jerry20091103/Teensy_Grovebox/Teensy_Grovebox_CODE/src/Audio/AudioSynth.cpp

#include "AudioSynth.h"
#include "AudioIO.h"
#include "SF2_Samples/SF2_Samples.h"
#include "AudioUtility.h"

AudioSynth_ AudioSynth;

AudioSynth_::ModParamList::ModParamList(AudioVoice *voiceArr) : oscPitchOffset{OscPitchOffset(voiceArr, 0), OscPitchOffset(voiceArr, 1)},
                                                                oscLevel{OscLevel(voiceArr, 0), OscLevel(voiceArr, 1)},
                                                                oscPwm{OscPwm(voiceArr, 0), OscPwm(voiceArr, 1)},
                                                                noiseLevel(voiceArr),
                                                                filterCutoff(voiceArr),
                                                                filterResonance(voiceArr),
                                                                lfoFreq{LfoFreq(voiceArr, 0), LfoFreq(voiceArr, 1)},
                                                                lfoLevel{LfoLevel(voiceArr, 0), LfoLevel(voiceArr, 1)},
                                                                envDelay{EnvDelay(voiceArr, 0), EnvDelay(voiceArr, 1), EnvDelay(voiceArr, 2)},
                                                                envAttack{EnvAttack(voiceArr, 0), EnvAttack(voiceArr, 1), EnvAttack(voiceArr, 2)},
                                                                envDecay{EnvDecay(voiceArr, 0), EnvDecay(voiceArr, 1), EnvDecay(voiceArr, 2)},
                                                                envSustain{EnvSustain(voiceArr, 0), EnvSustain(voiceArr, 1), EnvSustain(voiceArr, 2)},
                                                                envRelease{EnvRelease(voiceArr, 0), EnvRelease(voiceArr, 1), EnvRelease(voiceArr, 2)},
                                                                clipLevel(voiceArr)
{
}

AudioSynth_::AudioSynth_()
    : modParamList(voiceArr)
{
    // set up voice mixers
    voiceMixer[0] = &voiceMixer0_0;
    voiceMixer[1] = &voiceMixer0_1;

    for (auto i : voiceMixer)
    {
        i->gain(0, 0.25);
        i->gain(1, 0.25);
        i->gain(2, 0.25);
        i->gain(3, 0.25);
    }

    voiceFinalMixer = &voiceMixer1_0;

    voiceFinalMixer->gain(0, 0.5);
    voiceFinalMixer->gain(1, 0.5);

    // setup master volume
    mainVolume[0] = &ampInsOutL;
    mainVolume[1] = &ampInsOutR;

    // *initiailze all voices
    // wavetable synth
    voiceArr[0].waveTable = &wavetable0;
    voiceArr[1].waveTable = &wavetable1;
    voiceArr[2].waveTable = &wavetable2;
    voiceArr[3].waveTable = &wavetable3;
    voiceArr[4].waveTable = &wavetable4;
    voiceArr[5].waveTable = &wavetable5;
    voiceArr[6].waveTable = &wavetable6;
    voiceArr[7].waveTable = &wavetable7;
    // 2 waveforms
    voiceArr[0].waveform[0] = &waveform0_0;
    voiceArr[0].waveform[1] = &waveform0_1;
    voiceArr[1].waveform[0] = &waveform1_0;
    voiceArr[1].waveform[1] = &waveform1_1;
    voiceArr[2].waveform[0] = &waveform2_0;
    voiceArr[2].waveform[1] = &waveform2_1;
    voiceArr[3].waveform[0] = &waveform3_0;
    voiceArr[3].waveform[1] = &waveform3_1;
    voiceArr[4].waveform[0] = &waveform4_0;
    voiceArr[4].waveform[1] = &waveform4_1;
    voiceArr[5].waveform[0] = &waveform5_0;
    voiceArr[5].waveform[1] = &waveform5_1;
    voiceArr[6].waveform[0] = &waveform6_0;
    voiceArr[6].waveform[1] = &waveform6_1;
    voiceArr[7].waveform[0] = &waveform7_0;
    voiceArr[7].waveform[1] = &waveform7_1;
    // noise generator
    voiceArr[0].noise = &noise0;
    voiceArr[1].noise = &noise1;
    voiceArr[2].noise = &noise2;
    voiceArr[3].noise = &noise3;
    voiceArr[4].noise = &noise4;
    voiceArr[5].noise = &noise5;
    voiceArr[6].noise = &noise6;
    voiceArr[7].noise = &noise7;
    // playClip (sample player)
    voiceArr[0].playClip = &playClip0;
    voiceArr[1].playClip = &playClip1;
    voiceArr[2].playClip = &playClip2;
    voiceArr[3].playClip = &playClip3;
    voiceArr[4].playClip = &playClip4;
    voiceArr[5].playClip = &playClip5;
    voiceArr[6].playClip = &playClip6;
    voiceArr[7].playClip = &playClip7;
    // clip amp (sampler volume)
    voiceArr[0].clipAmp = &clipAmp0;
    voiceArr[1].clipAmp = &clipAmp1;
    voiceArr[2].clipAmp = &clipAmp2;
    voiceArr[3].clipAmp = &clipAmp3;
    voiceArr[4].clipAmp = &clipAmp4;
    voiceArr[5].clipAmp = &clipAmp5;
    voiceArr[6].clipAmp = &clipAmp6;
    voiceArr[7].clipAmp = &clipAmp7;
    // voice mode switch
    voiceArr[0].voiceSwitch = &voiceSwitch0;
    voiceArr[1].voiceSwitch = &voiceSwitch1;
    voiceArr[2].voiceSwitch = &voiceSwitch2;
    voiceArr[3].voiceSwitch = &voiceSwitch3;
    voiceArr[4].voiceSwitch = &voiceSwitch4;
    voiceArr[5].voiceSwitch = &voiceSwitch5;
    voiceArr[6].voiceSwitch = &voiceSwitch6;
    voiceArr[7].voiceSwitch = &voiceSwitch7;
    // ladder filter
    voiceArr[0].ladderFilter = &ladder0;
    voiceArr[1].ladderFilter = &ladder1;
    voiceArr[2].ladderFilter = &ladder2;
    voiceArr[3].ladderFilter = &ladder3;
    voiceArr[4].ladderFilter = &ladder4;
    voiceArr[5].ladderFilter = &ladder5;
    voiceArr[6].ladderFilter = &ladder6;
    voiceArr[7].ladderFilter = &ladder7;
    // lfo1
    voiceArr[0].lfo[0] = &lfo0_0;
    voiceArr[1].lfo[0] = &lfo1_0;
    voiceArr[2].lfo[0] = &lfo2_0;
    voiceArr[3].lfo[0] = &lfo3_0;
    voiceArr[4].lfo[0] = &lfo4_0;
    voiceArr[5].lfo[0] = &lfo5_0;
    voiceArr[6].lfo[0] = &lfo6_0;
    voiceArr[7].lfo[0] = &lfo7_0;
    // lfo2
    voiceArr[0].lfo[1] = &lfo0_1;
    voiceArr[1].lfo[1] = &lfo1_1;
    voiceArr[2].lfo[1] = &lfo2_1;
    voiceArr[3].lfo[1] = &lfo3_1;
    voiceArr[4].lfo[1] = &lfo4_1;
    voiceArr[5].lfo[1] = &lfo5_1;
    voiceArr[6].lfo[1] = &lfo6_1;
    voiceArr[7].lfo[1] = &lfo7_1;
    // amp envelope
    voiceArr[0].env[0] = &ampEnvelope0;
    voiceArr[1].env[0] = &ampEnvelope1;
    voiceArr[2].env[0] = &ampEnvelope2;
    voiceArr[3].env[0] = &ampEnvelope3;
    voiceArr[4].env[0] = &ampEnvelope4;
    voiceArr[5].env[0] = &ampEnvelope5;
    voiceArr[6].env[0] = &ampEnvelope6;
    voiceArr[7].env[0] = &ampEnvelope7;
    // env1
    voiceArr[0].env[1] = &envelope0_0;
    voiceArr[1].env[1] = &envelope1_0;
    voiceArr[2].env[1] = &envelope2_0;
    voiceArr[3].env[1] = &envelope3_0;
    voiceArr[4].env[1] = &envelope4_0;
    voiceArr[5].env[1] = &envelope5_0;
    voiceArr[6].env[1] = &envelope6_0;
    voiceArr[7].env[1] = &envelope7_0;
    // env2
    voiceArr[0].env[2] = &envelope0_1;
    voiceArr[1].env[2] = &envelope1_1;
    voiceArr[2].env[2] = &envelope2_1;
    voiceArr[3].env[2] = &envelope3_1;
    voiceArr[4].env[2] = &envelope4_1;
    voiceArr[5].env[2] = &envelope5_1;
    voiceArr[6].env[2] = &envelope6_1;
    voiceArr[7].env[2] = &envelope7_1;
    // lfoSample[0]
    voiceArr[0].lfoSample[0] = &lfoSample0_0;
    voiceArr[1].lfoSample[0] = &lfoSample1_0;
    voiceArr[2].lfoSample[0] = &lfoSample2_0;
    voiceArr[3].lfoSample[0] = &lfoSample3_0;
    voiceArr[4].lfoSample[0] = &lfoSample4_0;
    voiceArr[5].lfoSample[0] = &lfoSample5_0;
    voiceArr[6].lfoSample[0] = &lfoSample6_0;
    voiceArr[7].lfoSample[0] = &lfoSample7_0;
    // lfoSample[1]
    voiceArr[0].lfoSample[1] = &lfoSample0_1;
    voiceArr[1].lfoSample[1] = &lfoSample1_1;
    voiceArr[2].lfoSample[1] = &lfoSample2_1;
    voiceArr[3].lfoSample[1] = &lfoSample3_1;
    voiceArr[4].lfoSample[1] = &lfoSample4_1;
    voiceArr[5].lfoSample[1] = &lfoSample5_1;
    voiceArr[6].lfoSample[1] = &lfoSample6_1;
    voiceArr[7].lfoSample[1] = &lfoSample7_1;
    // envSample[0]
    voiceArr[0].envSample[0] = &envSample0_0;
    voiceArr[1].envSample[0] = &envSample1_0;
    voiceArr[2].envSample[0] = &envSample2_0;
    voiceArr[3].envSample[0] = &envSample3_0;
    voiceArr[4].envSample[0] = &envSample4_0;
    voiceArr[5].envSample[0] = &envSample5_0;
    voiceArr[6].envSample[0] = &envSample6_0;
    voiceArr[7].envSample[0] = &envSample7_0;
    // envSample[1]
    voiceArr[0].envSample[1] = &envSample0_1;
    voiceArr[1].envSample[1] = &envSample1_1;
    voiceArr[2].envSample[1] = &envSample2_1;
    voiceArr[3].envSample[1] = &envSample3_1;
    voiceArr[4].envSample[1] = &envSample4_1;
    voiceArr[5].envSample[1] = &envSample5_1;
    voiceArr[6].envSample[1] = &envSample6_1;
    voiceArr[7].envSample[1] = &envSample7_1;
    // ampEnvSample
    voiceArr[0].ampEnvSample = &ampEnvSample0;
    voiceArr[1].ampEnvSample = &ampEnvSample1;
    voiceArr[2].ampEnvSample = &ampEnvSample2;
    voiceArr[3].ampEnvSample = &ampEnvSample3;
    voiceArr[4].ampEnvSample = &ampEnvSample4;
    voiceArr[5].ampEnvSample = &ampEnvSample5;
    voiceArr[6].ampEnvSample = &ampEnvSample6;
    voiceArr[7].ampEnvSample = &ampEnvSample7;

    // set env1 and env2 DC generator
    envDc0.amplitude(1);
    envDc1.amplitude(1);
    envDc2.amplitude(1);
    envDc3.amplitude(1);
    envDc4.amplitude(1);
    envDc5.amplitude(1);
    envDc6.amplitude(1);
    envDc7.amplitude(1);

    setSF2Instrument(0);
    setOscWaveform(0, WAVE_OSC_SINE);
    setOscWaveform(1, WAVE_OSC_SINE);
    setVoiceMode(VOICE_MODE_WAVETABLE);

    for (int i = 0; i < MAX_VOICE; i++)
    {
        // put voice in idle list
        idleNote.push_front(noteEntry(0, i));
    }
}

void AudioSynth_::calAndSetOscPitchOffset(uint8_t id)
{
    float freqOffset = 0.0f;
    if (oscOctave[id] || oscSemi[id] || oscDetune[id])
    {
        // the modulation range is 4 octaves, we convert the offset to -1 to 1 range in 4 octaves.
        freqOffset = (oscOctave[id] + (((float)oscSemi[id] + oscDetune[id]) / 12.0f)) / 4.0f;
    }
    modParamList.oscPitchOffset[id].set(freqOffset);
}

void AudioSynth_::noteOn(uint8_t note)
{
    int16_t voiceFound = -1;
    // check if the note is already playing
    for (std::list<noteEntry>::iterator it = playingNote.begin(); it != playingNote.end(); it++)
    {
        if (it->note == note)
        {
            voiceFound = it->voiceIndex;
            playingNote.erase(it);
            voiceArr[voiceFound].noteOff();

            break;
        }
    }
    if (voiceFound == -1)
    {
        // If the note is not playig, take the last note from idleNote list.
        if (!idleNote.empty())
        {
            voiceFound = idleNote.back().voiceIndex;
            idleNote.pop_back();
        }
        // If the all voices are occupied, grab the last voice from playing list.
        else if (!playingNote.empty())
        {
            voiceFound = playingNote.back().voiceIndex;
            playingNote.pop_back();
            voiceArr[voiceFound].noteOff();
        }
    }
    // DEBUG
    if (voiceFound == -1)
        return;

    playingNote.push_front(noteEntry(note, voiceFound));
    voiceArr[voiceFound].isNoteOn = true;
    if (useVelocity)
        voiceArr[voiceFound].noteOn(note, map(velocity, 0, 1, 0.2, 1));
    else
        voiceArr[voiceFound].noteOn(note, 0.8);

    // apply oscPitchOffset to synth OSCs
    if (curVoiceMode == VOICE_MODE_SYNTH)
    {
        calAndSetOscPitchOffset(0);
        calAndSetOscPitchOffset(1);
    }
}

void AudioSynth_::noteOff(uint8_t note)
{
    // Check if the note is already playing.
    for (std::list<noteEntry>::iterator it = playingNote.begin(); it != playingNote.end(); it++)
    {
        if (it->note == note)
        {
            uint8_t voiceInd = it->voiceIndex;
            voiceArr[voiceInd].isNoteOn = false;
            // If sustaining, set isNoteOn = false, and let it play in playingNote (don't stop it)
            // Stop the note if not sustaining.
            if (!isSustain)
            {
                playingNote.erase(it);
                idleNote.push_front(noteEntry(note, voiceInd));
                voiceArr[voiceInd].noteOff();
            }
            break;
        }
    }
    // If not, then it may be stolen by other notes. Nothing to do here.
}

void AudioSynth_::sustainOn()
{
    isSustain = true;
}

void AudioSynth_::sustainOff()
{
    isSustain = false;
    // Find all notes in playingNotes that are noteOff (the key was released but is sustaining).
    for (std::list<noteEntry>::iterator it = playingNote.begin(); it != playingNote.end();)
    {
        uint8_t voiceInd = it->voiceIndex;
        if (!voiceArr[voiceInd].isNoteOn)
        {
            // remove the note from playingNote list and stop it.
            playingNote.erase(it++);
            idleNote.push_front(noteEntry(0, voiceInd));
            voiceArr[voiceInd].noteOff();

            if (playingNote.empty())
                break;
        }
        else
        {
            it++; // the iterator increment is moved here because after erase(), "it" becomes invalid.
        }
    }
}

// find all playing notes and set their pitch bend
void AudioSynth_::pitchbend(float semitone, float amount)
{
    curPitchbend = amount;
    curPitchbendMult = pow(2.0f, semitone / 12.0f);
    for (uint8_t i = 0; i < MAX_VOICE; i++)
    {
        voiceArr[i].setPitchbend(curPitchbendMult);
        // apply the pitcbend to the oscillators (force update modulation)
        modParamList.oscPitchOffset[0].modulate(i, modParamList.oscPitchOffset[0].getModValue(i));
        modParamList.oscPitchOffset[1].modulate(i, modParamList.oscPitchOffset[1].getModValue(i));
        // apply pitchbend to sampler
        voiceArr[i].setSampleNoteOffset(semitone);
    }
}

void AudioSynth_::modwheel(float amount)
{
    curModWheel = amount;
}

void AudioSynth_::setMasterVol(int8_t vol)
{
    float gain = dBtoGain(vol);
    mainVolume[0]->gain(gain);
    mainVolume[1]->gain(gain);
}

void AudioSynth_::setUseVelocity(bool value)
{
    useVelocity = value;
}

void AudioSynth_::setSF2Instrument(uint8_t id)
{
    if (id < MAX_SF2_INSTRUMENTS)
    {
        for (int i = 0; i < MAX_VOICE; i++)
        {
            voiceArr[i].setInstrument(*SF2_InstrumentRef[id]);
        }
    }
}

void AudioSynth_::setVoiceMode(uint8_t mode)
{
    curVoiceMode = mode;
    if (mode == VOICE_MODE_SYNTH)
    {
        // turn on the oscillators
        modParamList.oscLevel[0].set(modParamList.oscLevel[0].get());
        modParamList.oscLevel[1].set(modParamList.oscLevel[1].get());
    }
    else
    {
        // turn off synth oscillators to save cpu
        for (int i = 0; i < MAX_VOICE; i++)
        {
            voiceArr[i].waveform[0]->amplitude(0);
            voiceArr[i].waveform[1]->amplitude(0);
        }
    }

    for (int i = 0; i < MAX_VOICE; i++)
    {
        voiceArr[i].setVoiceMode(mode);
    }
}

void AudioSynth_::setOscWaveform(uint8_t id, uint8_t wave)
{
    for (int i = 0; i < MAX_VOICE; i++)
    {
        voiceArr[i].setOscWaveform(id, wave);
    }
}

void AudioSynth_::setOscOctave(uint8_t id, int8_t value)
{
    oscOctave[id] = value;
    calAndSetOscPitchOffset(id);
}

void AudioSynth_::setOscSemi(uint8_t id, int8_t value)
{
    oscSemi[id] = value;
    calAndSetOscPitchOffset(id);
}

void AudioSynth_::setOscPwm(uint8_t id, uint8_t duty)
{
    modParamList.oscPwm[id].set(duty * 0.01f);
}

void AudioSynth_::setOscDetune(uint8_t id, float amount)
{
    oscDetune[id] = amount;
    calAndSetOscPitchOffset(id);
}

void AudioSynth_::setOscLevel(uint8_t id, uint8_t amount)
{
    // block level change if not in synth mode (to keep oscillators off)
    if (curVoiceMode != VOICE_MODE_SYNTH)
        return;

    float gain;
    if (amount > 0)
        gain = dBtoGain(amount * 0.5f - 60); // the max level is -10 dB, to prevent clipping.
    else
        gain = 0;
    modParamList.oscLevel[id].set(gain);
}

void AudioSynth_::setNoiseLevel(float amount)
{
    float gain;
    if (amount > 0)
        gain = dBtoGain(amount * 0.5f - 60); // the max level is -10 dB, to prevent clipping.
    else
        gain = 0;
    modParamList.noiseLevel.set(gain);
}

void AudioSynth_::setLadderFreq(float freq)
{
    modParamList.filterCutoff.set(freq);
}

// set the ladder filter resonance. range 0~1.
void AudioSynth_::setLadderResonance(float amount)
{
    modParamList.filterResonance.set(map(amount, 0, 1, 0, 1.8));
}

// set the ladder filter drive. range 0~1.
void AudioSynth_::setLadderDrive(float amount)
{
    float drive = map(amount, 0, 1, 1, 4);
    for (int i = 0; i < MAX_VOICE; i++)
    {
        voiceArr[i].setLadderDrive(drive);
    }
}

// set the ladder filter passband gain. range 0~1.
void AudioSynth_::setLadderPassbandGain(float amount)
{
    float gain = map(amount, 0, 1, 0, 0.5);
    for (int i = 0; i < MAX_VOICE; i++)
    {
        voiceArr[i].setLadderPassbandGain(gain);
    }
}

void AudioSynth_::setLfoWaveform(uint8_t id, uint8_t wave)
{
    for (int i = 0; i < MAX_VOICE; i++)
    {
        voiceArr[i].setLfoWaveform(id, wave);
    }
}

void AudioSynth_::setLfoFreq(uint8_t id, float freq)
{
    modParamList.lfoFreq[id].set(freq);
}

void AudioSynth_::setLfoLevel(uint8_t id, float level)
{
    modParamList.lfoLevel[id].set(level);
}

// set the envelope delay time in ms (max 10000)
// id: 0 for amp envelope, 1~2 for modulation envelopes
void AudioSynth_::setEnvDelay(uint8_t id, float delay)
{
    modParamList.envDelay[id].set(delay);
}

// set the envelope attack time in ms (max 10000)
// id: 0 for amp envelope, 1~2 for modulation envelopes
void AudioSynth_::setEnvAttack(uint8_t id, float attack)
{
    modParamList.envAttack[id].set(attack);
}

// set the envelope decay time in ms (max 10000)
// id: 0 for amp envelope, 1~2 for modulation envelopes
void AudioSynth_::setEnvDecay(uint8_t id, float decay)
{
    modParamList.envDecay[id].set(decay);
}

// set the envelope sustain (0~1)
// id: 0 for amp envelope, 1~2 for modulation envelopes
void AudioSynth_::setEnvSustain(uint8_t id, float sustain)
{
    modParamList.envSustain[id].set(sustain);
}

// set the envelope release time in ms (max 10000)
// id: 0 for amp envelope, 1~2 for modulation envelopes
void AudioSynth_::setEnvRelease(uint8_t id, float release)
{
    modParamList.envRelease[id].set(release);
}

void AudioSynth_::setModulationListPtr(std::list<ModulationEntry> *list)
{
    modList = list;
}

// add a modulation to the modList and returns id. Returns -1 if not valid.
int8_t AudioSynth_::addModulation(uint8_t source, uint8_t dest)
{
    if (modList == nullptr)
        return -1;
    if (source < MOD_SRC_MAX && dest < MOD_TGT_MAX && modList->size() < MAX_MODULATION_COUNT)
    {
        modList->push_back(ModulationEntry((modSource)source, (modTarget)dest, 0));
        return modList->size() - 1;
    }
    return -1;
}

// set the id-th modulation amount of the modList
void AudioSynth_::setModulationAmount(uint8_t id, float amount)
{
    if (modList == nullptr)
        return;
    if (id < modList->size())
    {
        // get the modulation entry in list
        std::list<ModulationEntry>::iterator it = modList->begin();
        for (int i = 0; i < id; i++)
        {
            it++;
        }
        // set the amount
        it->amount = amount;
    }
}

// set the id-th modulation source of the modList
void AudioSynth_::setModulationSource(uint8_t id, uint8_t source)
{
    if (modList == nullptr)
        return;
    if (id < modList->size())
    {
        // get the modulation entry in list
        std::list<ModulationEntry>::iterator it = modList->begin();
        for (int i = 0; i < id; i++)
        {
            it++;
        }
        // set the source
        it->source = (modSource)source;
    }
}

// set the id-th modulation target of the modList
void AudioSynth_::setModulationTarget(uint8_t id, uint8_t target)
{
    if (modList == nullptr)
        return;
    if (id < modList->size())
    {
        // get the modulation entry in list
        std::list<ModulationEntry>::iterator it = modList->begin();
        for (int i = 0; i < id; i++)
        {
            it++;
        }
        // reset the previous target
        resetModulation(it->target);
        // set the target
        it->target = (modTarget)target;
    }
}

// reset the id-th modulation of the modList
void AudioSynth_::resetModulation(uint8_t id)
{
    if (id != MOD_TGT_NONE && id < MOD_TGT_MAX)
        modParamList[id].resetModulation();
}

// remove the id-th modulation of the modList
void AudioSynth_::removeModulation(uint8_t id)
{
    if (modList == nullptr)
        return;
    if (id < modList->size())
    {
        // get the modulation entry in list
        std::list<ModulationEntry>::iterator it = modList->begin();
        for (int i = 0; i < id; i++)
        {
            it++;
        }
        // reset the modulated target value
        resetModulation(it->target);
        // remove the entry
        modList->erase(it);
    }
}

void AudioSynth_::updateModulation()
{
    if (curVoiceMode != VOICE_MODE_SYNTH)
        return;

    if (modList == nullptr)
        return;

    for (uint8_t voiceId = 0; voiceId < MAX_VOICE; voiceId++)
    {
        float modSrcValue[MOD_SRC_MAX] = {0.0f};
        float modTgtValue[MOD_TGT_MAX] = {0.0f};
        bool dirty[MOD_TGT_MAX] = {false};
        // get all modulation source value and store it
        // TODO: need refactoring
        for (uint8_t i = 1; i < MOD_SRC_MAX; i++)
        {
            switch (i)
            {
            case MOD_SRC_LFO1:
                modSrcValue[i] = voiceArr[voiceId].lfoSample[0]->readSample() / 32768.0f;
                break;
            case MOD_SRC_LFO2:
                modSrcValue[i] = voiceArr[voiceId].lfoSample[1]->readSample() / 32768.0f;
                break;
            case MOD_SRC_AMPENV:
                modSrcValue[i] = voiceArr[voiceId].ampEnvSample->readSample() / 32768.0f;
                break;
            case MOD_SRC_ENV1:
                modSrcValue[i] = voiceArr[voiceId].envSample[0]->readSample() / 32768.0f;
                break;
            case MOD_SRC_ENV2:
                modSrcValue[i] = voiceArr[voiceId].envSample[1]->readSample() / 32768.0f;
                break;
            case MOD_SRC_PITCHBEND:
                modSrcValue[i] = curPitchbend;
                break;
            case MOD_SRC_MODWHEEL:
                modSrcValue[i] = curModWheel;
                break;
            case MOD_SRC_PITCH:
                modSrcValue[i] = (voiceArr[voiceId].curNote - 64) / 64.0f;
                break;
            case MOD_SRC_VELOCITY:
                modSrcValue[i] = voiceArr[voiceId].curAmp;
                break;
            }
        }

        // process all the modulations in modList, store the result value in modTgtValue
        for (std::list<ModulationEntry>::iterator it = modList->begin(); it != modList->end(); it++)
        {
            float value = modSrcValue[it->source];
            // calculate amount
            value *= it->amount;
            // add to the target value storege (using +=, so one target and be affected by multiple sources)
            modTgtValue[it->target] += value;
            // mark dirty
            dirty[it->target] = true;
        }
        // set the final modulation value to the targets
        for (uint8_t i = 1; i < MOD_TGT_MAX; i++)
        {
            if (dirty[i])
            {
                modParamList[i].modulate(voiceId, modTgtValue[i]);
            }
        }
    }
}

void AudioSynth_::playClip()
{
    for (uint8_t i = 0; i < MAX_VOICE; i++)
    {
        voiceArr[i].noteOn(60); // the note number is not used in sample editor mode
    }
}
void AudioSynth_::stopClip()
{
    for (uint8_t i = 0; i < MAX_VOICE; i++)
    {
        voiceArr[i].noteOff();
    }
}
void AudioSynth_::setClip(audio_block_data_t *data, uint16_t len)
{
    for (uint8_t i = 0; i < MAX_VOICE; i++)
    {
        voiceArr[i].playClip->setClip(data, len);
    }
}
void AudioSynth_::setClipLoop(bool loop)
{
    for (uint8_t i = 0; i < MAX_VOICE; i++)
    {
        voiceArr[i].playClip->loop(loop);
    }
}

void AudioSynth_::setClipStartPoint(float start)
{
    for (uint8_t i = 0; i < MAX_VOICE; i++)
    {
        voiceArr[i].playClip->setStartPoint(start);
    }
}
void AudioSynth_::setClipLoopStartPoint(float start)
{
    for (uint8_t i = 0; i < MAX_VOICE; i++)
    {
        voiceArr[i].playClip->setLoopStartPoint(start);
    }
}
void AudioSynth_::setClipLoopEndPoint(float end)
{
    for (uint8_t i = 0; i < MAX_VOICE; i++)
    {
        voiceArr[i].playClip->setLoopEndPoint(end);
    }
}
void AudioSynth_::setClipEndPoint(float end)
{
    for (uint8_t i = 0; i < MAX_VOICE; i++)
    {
        voiceArr[i].playClip->setEndPoint(end);
    }
}

void AudioSynth_::setClipLoopCrossfade(float crossfade)
{
    for (uint8_t i = 0; i < MAX_VOICE; i++)
    {
        voiceArr[i].playClip->setLoopCrossFade(crossfade);
    }
}

void AudioSynth_::setClipLevel(uint8_t amount)
{
    float gain;
    if (amount > 0)
        gain = dBtoGain(amount * 0.5f - 50); // the max level is 0 dB
    else
        gain = 0;

    modParamList.clipLevel.set(gain);
}

void AudioSynth_::setClipBaseNote(uint8_t note)
{
    for (uint8_t i = 0; i < MAX_VOICE; i++)
    {
        voiceArr[i].setSampleBaseNote(note);
    }
}
