jerry20091103/Teensy_Grovebox/Teensy_Grovebox_CODE/src/Audio/AudioVoice.cpp

#include "AudioVoice.h"
#include "AudioUtility.h"
#include "AudioSynth.h"

AudioVoice::AudioVoice()
{
}

void AudioVoice::setOscFreq(uint8_t id, float freq)
{
    waveform[id]->frequency(freq);
}

void AudioVoice::noteOn(uint8_t note, float amp)
{
    frequency = noteToFreq(note);
    curNote = note;
    curAmp = amp;
    switch (curVoiceMode)
    {
    case VOICE_MODE_SYNTH:
        setOscFreq(0, frequency);
        setOscFreq(1, frequency);
        // todo: use another amplitude object for velocity
        // waveform[0]->amplitude(amp);
        // waveform[1]->amplitude(amp);
        env[0]->noteOn();
        env[1]->noteOn();
        env[2]->noteOn();
        setSampleNoteOffset(curSampleNoteOffset);
        playClip->play();
        break;

    case VOICE_MODE_WAVETABLE:
        waveTable->playFrequency(frequency);
        waveTable->amplitude(amp);
        break;
    case VOICE_MODE_SAMPLE_EDITER:
        playClip->setSpeed(1);
        playClip->play();
    }
}

void AudioVoice::noteOff()
{
    switch (curVoiceMode)
    {
    case VOICE_MODE_SYNTH:
        env[0]->noteOff();
        env[1]->noteOff();
        env[2]->noteOff();
        playClip->noteOff();
        break;

    case VOICE_MODE_WAVETABLE:
        waveTable->stop();
        break;
    case VOICE_MODE_SAMPLE_EDITER:
        playClip->stop();
        break;
    }
}

// set the amount of pitch bend in semitones
void AudioVoice::setPitchbend(float pitchMult)
{
    curPitchBendMult = pitchMult;
    switch (curVoiceMode)
    {
    case VOICE_MODE_SYNTH:
        // do nothing for now
        break;

    case VOICE_MODE_WAVETABLE:
        waveTable->setFrequency(frequency * pitchMult); // ! for unknown reason, program crashes when the voice is not played once then setFrequency() is set
        break;
    }
}

// use the audio mixer to select voice mode (soucre of voice)
void AudioVoice::setVoiceMode(uint8_t mode)
{
    curVoiceMode = mode;
    for (uint8_t i = 0; i < 4; i++)
    {
        if (i == mode)
        {
            voiceSwitch->gain(i, 1.0f);
        }
        else
        {
            voiceSwitch->gain(i, 0.0f);
        }
    }
}

// set the output waveform of the synth voice
void AudioVoice::setOscWaveform(uint8_t id, uint8_t wave)
{
    switch (wave)
    {
    case WAVE_OSC_SINE:
        waveform[id]->begin(WAVEFORM_SINE);
        break;
    case WAVE_OSC_TRIANGLE:
        waveform[id]->begin(WAVEFORM_TRIANGLE);
        break;
    case WAVE_OSC_SAW:
        waveform[id]->begin(WAVEFORM_BANDLIMIT_SAWTOOTH);
        break;
    case WAVE_OSC_SQUARE:
        waveform[id]->begin(WAVEFORM_BANDLIMIT_PULSE);
        break;
    }
}

void AudioVoice::setLfoWaveform(uint8_t id, uint8_t wave)
{
    switch (wave)
    {
    case WAVE_LFO_SINE:
        lfo[id]->begin(WAVEFORM_SINE);
        break;
    case WAVE_LFO_TRIANGLE:
        lfo[id]->begin(WAVEFORM_TRIANGLE);
        break;
    case WAVE_LFO_SAW:
        lfo[id]->begin(WAVEFORM_BANDLIMIT_SAWTOOTH);
        break;
    case WAVE_LFO_SAW_REV:
        lfo[id]->begin(WAVEFORM_BANDLIMIT_SAWTOOTH_REVERSE);
        break;
    case WAVE_LFO_SQUARE:
        lfo[id]->begin(WAVEFORM_BANDLIMIT_PULSE);
        break;
    case WAVE_LFO_SAMPLE_HOLD:
        lfo[id]->begin(WAVEFORM_SAMPLE_HOLD);
        break;
    }
}

void AudioVoice::setSampleBaseNote(uint8_t note)
{
    curSampleBaseNote = note;
    setSampleNoteOffset(curSampleNoteOffset);
}

void AudioVoice::setSampleNoteOffset(float offset)
{
    curSampleNoteOffset = offset;
    playClip->setSpeed(powf(2, (curNote - curSampleBaseNote + curSampleNoteOffset) / 12.0f));
}
