jerry20091103/Teensy_Grovebox/Teensy_Grovebox_CODE/src/GuiObjects/Colors.h

#ifndef COLORS_H
#define COLORS_H

#include "lvgl.h"

// * Global Colors
static const lv_color_t color_Red = lv_palette_main(LV_PALETTE_RED);
static const lv_color_t color_RedDark = lv_color_hex(0x8c1515);
static const lv_color_t color_Yellow = lv_palette_main(LV_PALETTE_YELLOW);
static const lv_color_t color_YellowDark = lv_color_hex(0xb58a14);
static const lv_color_t color_Blue = lv_palette_main(LV_PALETTE_BLUE);
static const lv_color_t color_BlueDark = lv_palette_darken(LV_PALETTE_BLUE, 4);
static const lv_color_t color_Green = lv_palette_main(LV_PALETTE_GREEN);
static const lv_color_t color_GreenDark = lv_palette_darken(LV_PALETTE_GREEN, 4);
static const lv_color_t color_Grey = lv_palette_darken(LV_PALETTE_GREY, 3);
static const lv_color_t color_GreyDark = lv_palette_darken(LV_PALETTE_GREY, 4);
static const lv_color_t color_LightGreen = lv_palette_main(LV_PALETTE_LIGHT_GREEN);
static const lv_color_t color_LightGreenDark = lv_palette_darken(LV_PALETTE_LIGHT_GREEN, 3);

#endif // COLORS_H
